nexxyz/cellSymphony/release-artifacts/enclosure/step/standoff_pillar_10mm.step

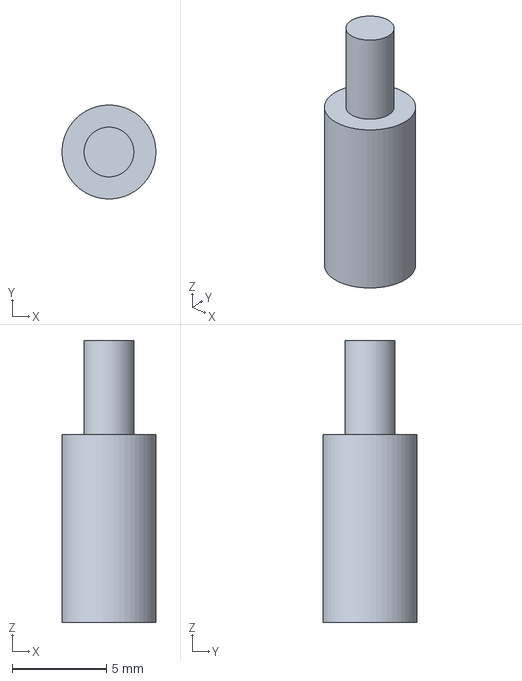
[picture p19: CAD file, 2026-07-09]
release-artifacts/enclosure/step/standoff_pillar_10mm.step
5.00 x 5.00 x 15.0 mm
