nexxyz/cellSymphony/release-artifacts/enclosure/step/standoff_top_pin_thin_base.step

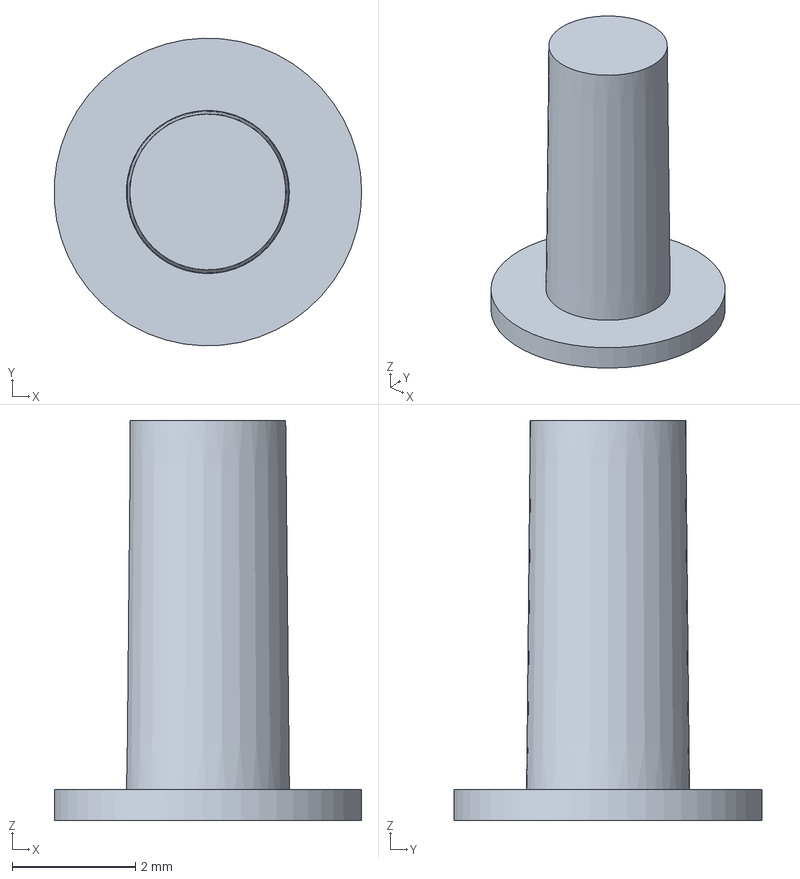
[picture p20: CAD file, 2026-07-08]
release-artifacts/enclosure/step/standoff_top_pin_thin_base.step
5.00 x 5.00 x 6.50 mm
