nexxyz/cellSymphony/release-artifacts/enclosure/3mf-multicolor/mx_keycap_play_multicolor_flush.3mf

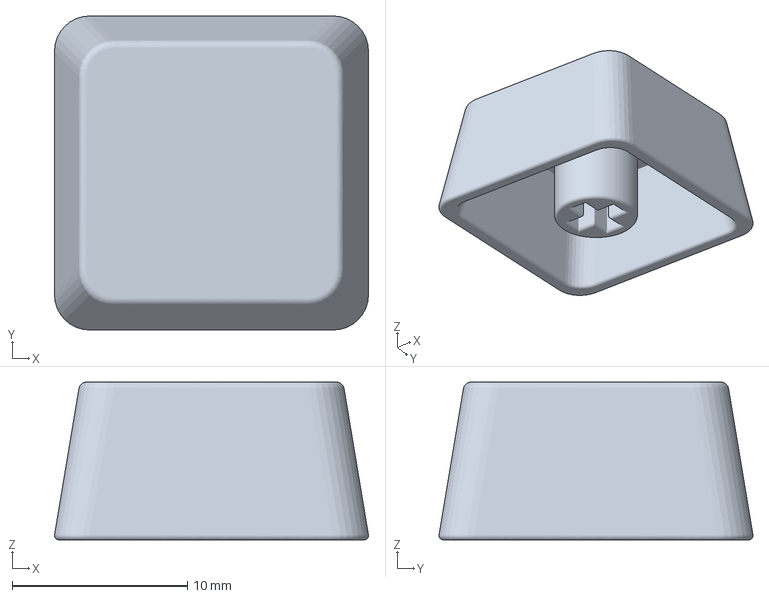
[picture p22: CAD file, 2026-07-10]
release-artifacts/enclosure/3mf-multicolor/mx_keycap_play_multicolor_flush.3mf
17.9 x 17.9 x 9.00 mm
