nexxyz/cellSymphony/userdocs/hardware/images/assembly/audio-breakout.jpg

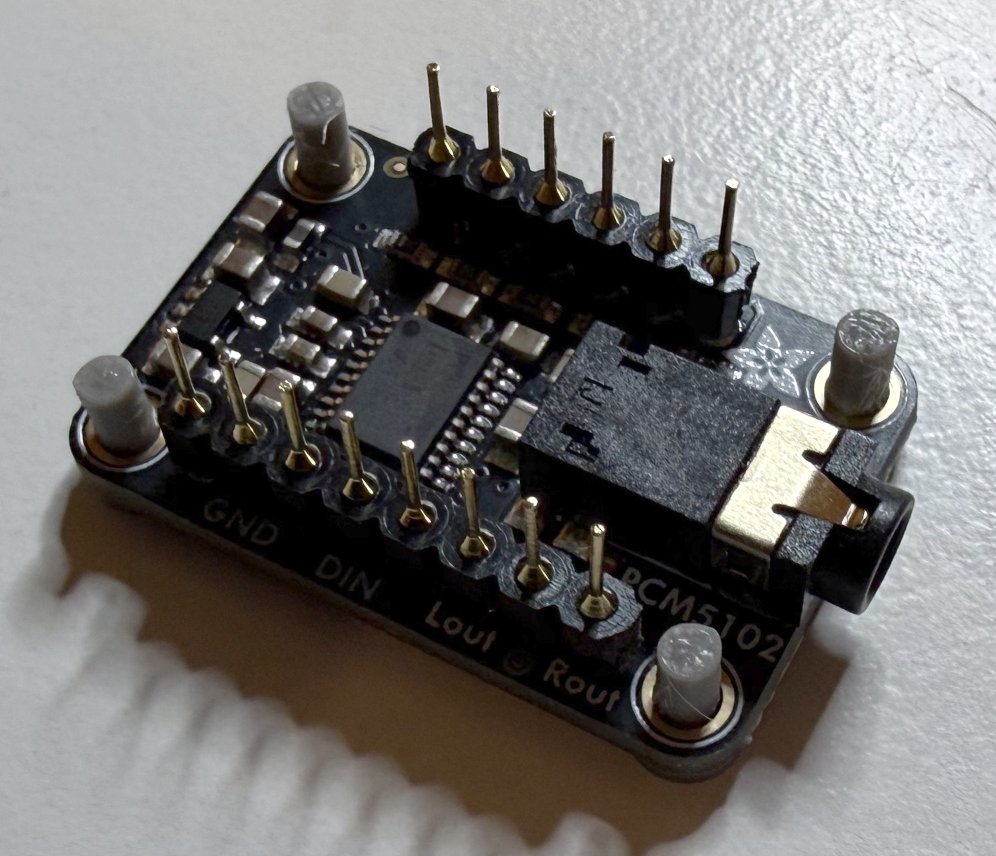
userdocs/hardware/images/assembly/audio-breakout.jpg
