nexxyz/cellSymphony/userdocs/hardware/images/assembly/neotrellis-address-jumpers.jpg

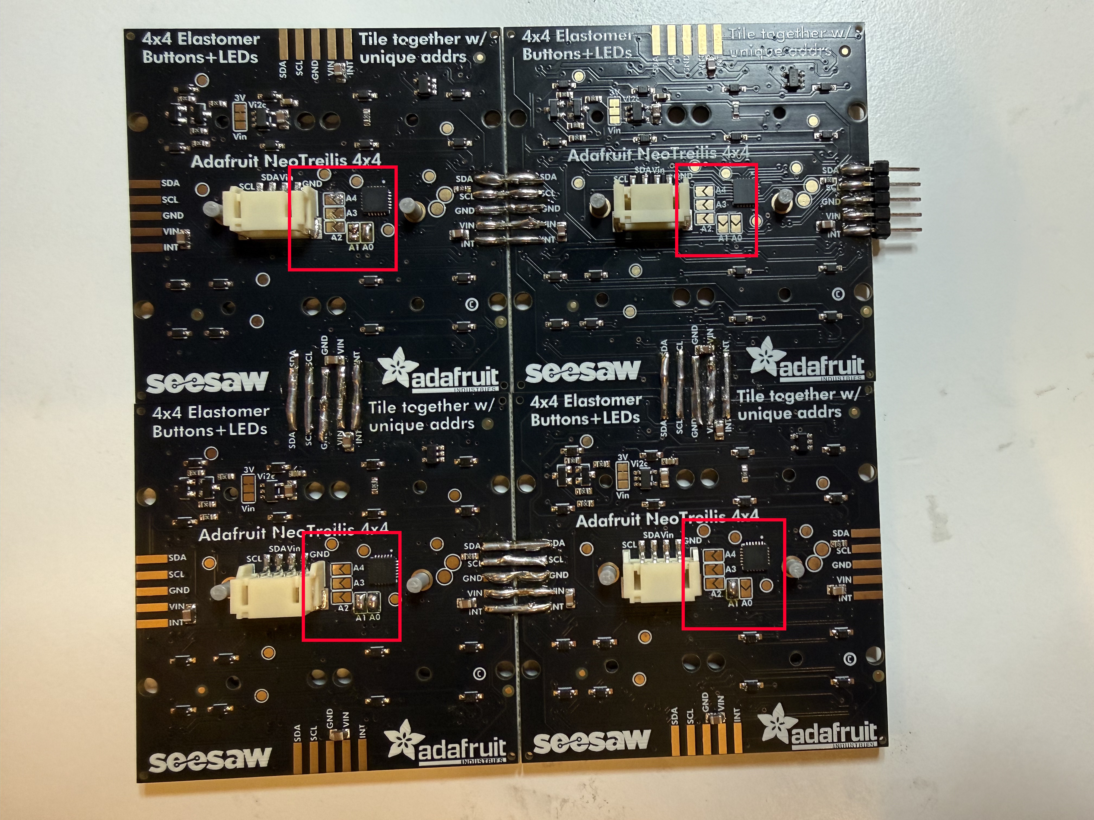
userdocs/hardware/images/assembly/neotrellis-address-jumpers.jpg
