nexxyz/cellSymphony/userdocs/hardware/images/assembly/oled.jpg

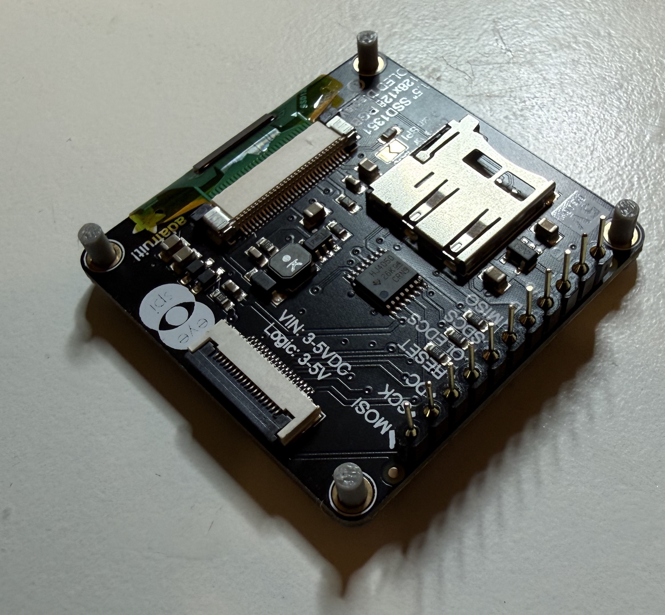
userdocs/hardware/images/assembly/oled.jpg
