nexxyz/cellSymphony/userdocs/hardware/images/assembly/rpi-content-repository.png

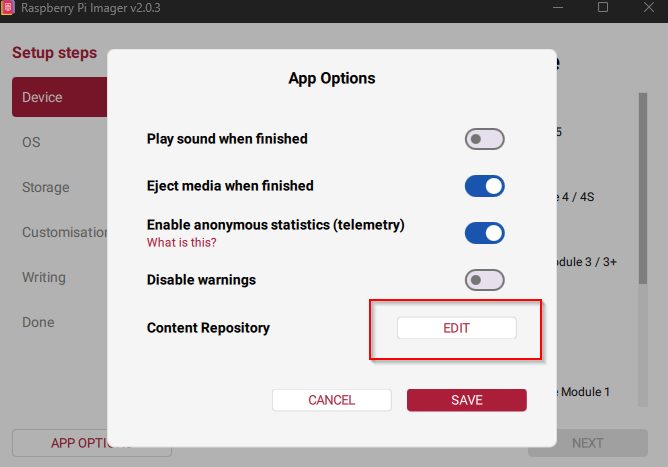
userdocs/hardware/images/assembly/rpi-content-repository.png
