nexxyz/cellSymphony/userdocs/hardware/images/assembly/rpi-imager-options.png

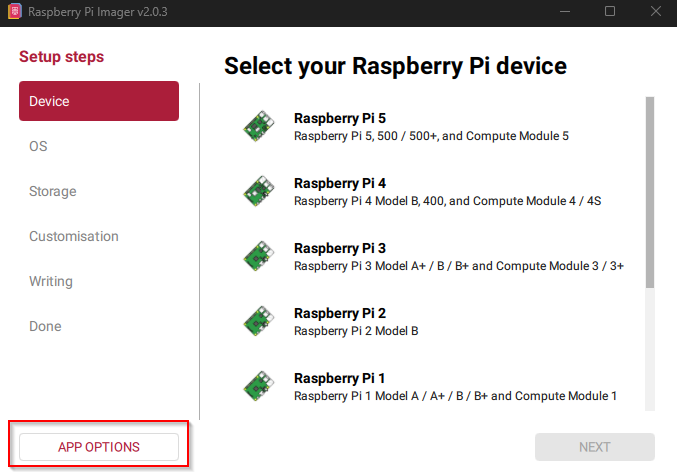
userdocs/hardware/images/assembly/rpi-imager-options.png
