nexxyz/cellSymphony/userdocs/hardware/images/assembly/rpi-repository-source.png

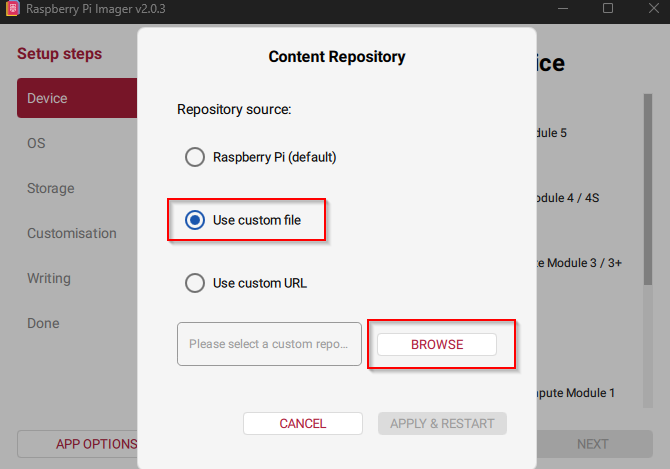
userdocs/hardware/images/assembly/rpi-repository-source.png
