nexxyz/cellSymphony/userdocs/hardware/images/assembly/soldered-pcb.jpg

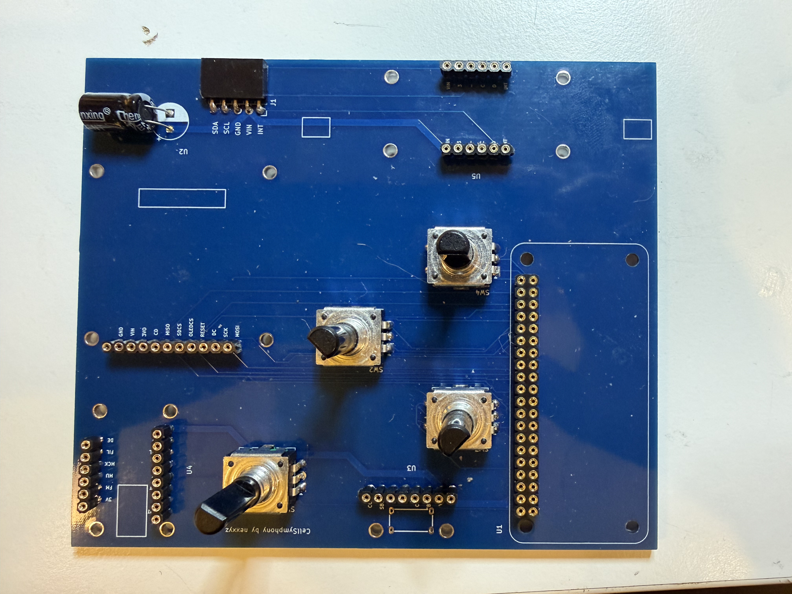
userdocs/hardware/images/assembly/soldered-pcb.jpg
