nexxyz/cellSymphony/apps/pi-zero/src/render.rs

use crate::seesaw_io::SeesawCommand;
use octessera_hal::OledSsd1351;
use platform_core::palette;
use playback_runtime::RuntimeUiPulse;
use serde_json::Value;
use std::sync::mpsc::Sender;
use std::time::{Duration, Instant};

pub(crate) mod hdmi;
mod oled;
mod sleep_leds;

pub(crate) use oled::OLED_FRAME_BYTES;
#[cfg(test)]
use oled::{glyph_rows, oled_frame};
use oled::{oled_frame_into, oled_signature};
use sleep_leds::{SleepLedAnimation, SleepLedFrames};

const SPLASH_BOOT: &[u8] = include_bytes!(concat!(env!("OUT_DIR"), "/splash_boot.rgb565"));
const SPLASH_SLEEP_SHUTDOWN: &[u8] =
    include_bytes!(concat!(env!("OUT_DIR"), "/splash_sleep_shutdown.rgb565"));
const SLEEP_DIM_SCALE: f32 = 0.08;
const MIN_SLEEP_DIM_SCALE: f32 = 0.04;

pub struct HardwareRenderTargets {
    pub oled: OledSsd1351,
    pub seesaw_tx: Sender<SeesawCommand>,
    pub hdmi: Option<hdmi::HdmiFramebuffer>,
}

pub struct HardwareRenderCache {
    led_frame: Option<[[u8; 3]; 64]>,
    neokey_colors: Option<[[u8; 3]; 4]>,
    sleep_leds: SleepLedAnimation,
    oled_signature: u64,
    oled_frame: Vec<u8>,
    hdmi_signature: u64,
    event_dot_until: Option<Instant>,
    transport_flash_until: Option<Instant>,
    transport_flash: Option<String>,
}

impl HardwareRenderCache {
    pub fn new() -> Self {
        Self {
            led_frame: None,
            neokey_colors: None,
            sleep_leds: SleepLedAnimation::new(),
            oled_signature: 0,
            oled_frame: vec![0_u8; OLED_FRAME_BYTES],
            hdmi_signature: 0,
            event_dot_until: None,
            transport_flash_until: None,
            transport_flash: None,
        }
    }

    pub fn apply_ui_pulse(&mut self, pulse: RuntimeUiPulse) {
        let now = Instant::now();
        match pulse {
            RuntimeUiPulse::TriggerPulse { duration_ms } => {
                self.event_dot_until = Some(now + Duration::from_millis(duration_ms));
            }
            RuntimeUiPulse::TransportFlash { flash, duration_ms } => {
                self.transport_flash = Some(flash);
                self.transport_flash_until = Some(now + Duration::from_millis(duration_ms));
            }
        }
    }

    pub fn snapshot_with_transients(&mut self, snapshot: &Value) -> Value {
        let now = Instant::now();
        let event_active = self.event_dot_until.is_some_and(|until| now < until);
        let transport_active = self.transport_flash_until.is_some_and(|until| now < until);
        if !event_active {
            self.event_dot_until = None;
        }
        if !transport_active {
            self.transport_flash_until = None;
            self.transport_flash = None;
        }
        if !event_active && !transport_active {
            return snapshot.clone();
        }
        let mut snapshot = snapshot.clone();
        if event_active {
            snapshot["eventDotOn"] = serde_json::json!(true);
        }
        if transport_active {
            if let Some(flash) = &self.transport_flash {
                snapshot["transportFlash"] = serde_json::json!(flash);
            }
        }
        snapshot
    }
}

impl Default for HardwareRenderCache {
    fn default() -> Self {
        Self::new()
    }
}

pub fn render_snapshot_cached(
    targets: &mut HardwareRenderTargets,
    snapshot: &Value,
    cache: &mut HardwareRenderCache,
) -> Option<Instant> {
    let animation_deadline = if snapshot_display_off(snapshot) {
        let now = Instant::now();
        let settings = snapshot.get("settings").unwrap_or(&Value::Null);
        let entered_sleep = cache.sleep_leds.enter(
            now,
            brightness_scale(settings.get("gridBrightness")),
            brightness_scale(settings.get("buttonBrightness")),
        );
        if entered_sleep {
            let frames = cache.sleep_leds.frames_at(now);
            send_sleep_led_frames(targets, cache, frames);
        } else if let Some(frames) = cache.sleep_leds.frames_if_due(now) {
            send_sleep_led_frames(targets, cache, frames);
        }
        cache.sleep_leds.next_deadline()
    } else {
        if cache.sleep_leds.active() {
            cache.clear_sleep_animation();
        }
        render_normal_leds(targets, snapshot, cache);
        None
    };

    let signature = oled_signature(snapshot);
    if cache.oled_signature != signature {
        cache.oled_signature = signature;
        render_oled(&mut targets.oled, snapshot, &mut cache.oled_frame);
    }

    if let Some(hdmi) = targets.hdmi.as_mut() {
        let signature = hdmi::hdmi_signature(snapshot);
        if cache.hdmi_signature != signature {
            cache.hdmi_signature = signature;
            hdmi.render(snapshot);
        }
    }
    animation_deadline
}

impl HardwareRenderCache {
    fn clear_sleep_animation(&mut self) {
        self.sleep_leds.stop();
        self.led_frame = None;
        self.neokey_colors = None;
    }

    pub(crate) fn render_sleep_tick(
        &mut self,
        targets: &mut HardwareRenderTargets,
        now: Instant,
    ) -> Option<Instant> {
        if !self.sleep_leds.active() {
            return None;
        }
        if let Some(frames) = self.sleep_leds.frames_if_due(now) {
            send_sleep_led_frames(targets, self, frames);
        }
        self.sleep_leds.next_deadline()
    }
}

fn render_normal_leds(
    targets: &mut HardwareRenderTargets,
    snapshot: &Value,
    cache: &mut HardwareRenderCache,
) {
    if let Some(frame) = led_frame(snapshot) {
        send_grid_frame(targets, cache, frame);
    }
    send_neokey_colors(targets, cache, neokey_colors(snapshot));
}

fn send_sleep_led_frames(
    targets: &mut HardwareRenderTargets,
    cache: &mut HardwareRenderCache,
    frames: SleepLedFrames,
) {
    send_grid_frame(targets, cache, frames.grid);
    send_neokey_colors(targets, cache, frames.keys);
}

fn send_grid_frame(
    targets: &mut HardwareRenderTargets,
    cache: &mut HardwareRenderCache,
    frame: [[u8; 3]; 64],
) {
    if cache.led_frame.as_ref() != Some(&frame)
        && targets
            .seesaw_tx
            .send(SeesawCommand::GridFrame(frame))
            .is_ok()
    {
        cache.led_frame = Some(frame);
    }
}

fn send_neokey_colors(
    targets: &mut HardwareRenderTargets,
    cache: &mut HardwareRenderCache,
    colors: [[u8; 3]; 4],
) {
    let previous = cache.neokey_colors.unwrap_or([[u8::MAX; 3]; 4]);
    if previous != colors
        && targets
            .seesaw_tx
            .send(SeesawCommand::NeoKeyColors(colors))
            .is_ok()
    {
        cache.neokey_colors = Some(colors);
    }
}

pub fn led_frame(snapshot: &Value) -> Option<[[u8; 3]; 64]> {
    let settings = snapshot.get("settings").unwrap_or(&Value::Null);
    let mut brightness = brightness_scale(settings.get("gridBrightness"));
    if settings
        .get("ledsDimmed")
        .and_then(Value::as_bool)
        .unwrap_or(false)
    {
        brightness = sleep_dim_brightness(brightness);
    }
    let Some(rgb) = snapshot.get("leds")?.get("rgb").and_then(Value::as_array) else {
        return legacy_led_frame(snapshot, brightness);
    };
    let mut frame = [[0_u8; 3]; 64];
    for (idx, cell) in frame.iter_mut().enumerate() {
        let offset = idx * 3;
        *cell = scale(
            [
                scaled_u8(rgb.get(offset)),
                scaled_u8(rgb.get(offset + 1)),
                scaled_u8(rgb.get(offset + 2)),
            ],
            brightness,
        );
    }
    Some(frame)
}

fn legacy_led_frame(snapshot: &Value, brightness: f32) -> Option<[[u8; 3]; 64]> {
    let cells = snapshot.get("leds")?.get("cells")?.as_array()?;
    let mut frame = [[0_u8; 3]; 64];
    for (idx, cell) in cells.iter().take(64).enumerate() {
        frame[idx] = scale(
            [
                scaled_u8(cell.get("r")),
                scaled_u8(cell.get("g")),
                scaled_u8(cell.get("b")),
            ],
            brightness,
        );
    }
    Some(frame)
}

pub fn neokey_colors(snapshot: &Value) -> [[u8; 3]; 4] {
    let settings = snapshot.get("settings").unwrap_or(&Value::Null);
    let mut button_scale = brightness_scale(settings.get("buttonBrightness"));
    if settings
        .get("ledsDimmed")
        .and_then(Value::as_bool)
        .unwrap_or(false)
    {
        button_scale = sleep_dim_brightness(button_scale);
    }
    let combined = settings
        .get("combinedModifierHeld")
        .and_then(Value::as_bool)
        .unwrap_or(false);
    let shift_held = settings
        .get("shiftHeld")
        .and_then(Value::as_bool)
        .unwrap_or(false);
    let fn_held = settings
        .get("fnHeld")
        .and_then(Value::as_bool)
        .unwrap_or(false);
    let flash = snapshot
        .get("transportFlash")
        .or_else(|| settings.get("transportFlash"))
        .and_then(Value::as_str)
        .unwrap_or("none");
    let icon = snapshot
        .get("transportIcon")
        .and_then(Value::as_str)
        .unwrap_or("stop");
    let back = scale(palette::RED, button_scale);
    let space = if icon == "stop" {
        scale(palette::RED, button_scale)
    } else if icon == "pause" {
        scale(palette::BLUE, button_scale)
    } else if flash == "measure" {
        scale(palette::GREEN, button_scale)
    } else if flash == "beat" {
        scale(palette::YELLOW, button_scale)
    } else {
        scale(dim(palette::GREEN, 3), button_scale)
    };
    let shift = if combined {
        scale(palette::BLUE, button_scale)
    } else if shift_held {
        scale(palette::YELLOW, button_scale)
    } else {
        scale(dim(palette::GRAY, 3), button_scale)
    };
    let func = if combined {
        scale(palette::BLUE, button_scale)
    } else if fn_held {
        scale(palette::YELLOW, button_scale)
    } else {
        scale(dim(palette::GRAY, 3), button_scale)
    };
    [back, space, shift, func]
}

fn render_oled(oled: &mut OledSsd1351, snapshot: &Value, frame: &mut [u8]) {
    let off = snapshot_display_off(snapshot);
    if !off {
        let _ = oled.display_on();
    }
    oled_frame_into(snapshot, frame);
    let _ = oled.write_frame(frame);
    if off {
        let _ = oled.display_off();
    }
}

pub fn render_boot_splash(oled: &mut OledSsd1351) {
    let _ = oled.display_on();
    let snapshot = serde_json::json!({
        "display": {
            "off": false,
            "splash": "startup",
            "toast": ""
        },
        "settings": { "displayBrightness": 100 }
    });
    let mut frame = vec![0_u8; OLED_FRAME_BYTES];
    render_oled(oled, &snapshot, &mut frame);
}

pub fn render_shutdown_splash(oled: &mut OledSsd1351) {
    let _ = oled.display_on();
    let snapshot = serde_json::json!({
        "display": {
            "off": false,
            "splash": "shutdown",
            "toast": ""
        },
        "settings": { "displayBrightness": 100 }
    });
    let mut frame = vec![0_u8; OLED_FRAME_BYTES];
    render_oled(oled, &snapshot, &mut frame);
}

fn snapshot_display_off(snapshot: &Value) -> bool {
    snapshot
        .get("display")
        .and_then(|display| display.get("off"))
        .and_then(Value::as_bool)
        .unwrap_or(false)
}

pub(crate) fn fault_oled_frame_into(lines: &[String], frame: &mut [u8], lit: bool) {
    oled::fault_frame_into(lines, frame, lit);
}

fn scaled_u8(value: Option<&Value>) -> u8 {
    value.and_then(Value::as_u64).unwrap_or(0).min(255) as u8
}

fn brightness_scale(value: Option<&Value>) -> f32 {
    value
        .and_then(Value::as_u64)
        .map(|value| value.min(100) as f32 / 100.0)
        .unwrap_or(1.0)
}

fn sleep_dim_brightness(brightness: f32) -> f32 {
    if brightness <= 0.0 {
        0.0
    } else {
        (brightness * SLEEP_DIM_SCALE).max(MIN_SLEEP_DIM_SCALE)
    }
}

#[rustfmt::skip]
pub(super) fn scale(rgb: [u8; 3], factor: f32) -> [u8; 3] { [
    ((rgb[0] as f32) * factor).round().clamp(0.0, 255.0) as u8,
    ((rgb[1] as f32) * factor).round().clamp(0.0, 255.0) as u8,
    ((rgb[2] as f32) * factor).round().clamp(0.0, 255.0) as u8,
] }

pub(super) fn dim(rgb: [u8; 3], divisor: u8) -> [u8; 3] {
    let divisor = divisor.max(1);
    [rgb[0] / divisor, rgb[1] / divisor, rgb[2] / divisor]
}

pub(super) fn rgb565(rgb: [u8; 3]) -> u16 {
    ((u16::from(rgb[0]) & 0xF8) << 8) | ((u16::from(rgb[1]) & 0xFC) << 3) | (u16::from(rgb[2]) >> 3)
}

#[cfg(test)]
mod tests;
