nexxyz/cellSymphony/crates/playback-runtime/src/native_menu/pulses_sections.rs

use super::{
    action_item, axis_binding_label, bool_item, enum_item, enum_item_from_strings, group,
    number_item, parameter_picker_group_numeric, selected_index, slot_option_selected,
    NativeLinkArpConfig, NativeLinkLfoConfig, NativeMenuAction, NativeMenuConfig, NativeMenuItem,
    NativePulsesLayerConfig,
};

pub(super) fn arp_group(prefix: &str, arp: &NativeLinkArpConfig) -> NativeMenuItem {
    group(
        "Arp",
        vec![
            enum_item(
                "Mode",
                format!("{prefix}.mode"),
                vec![
                    "none",
                    "direct",
                    "up",
                    "down",
                    "bounce",
                    "outside_in",
                    "rotating",
                    "random",
                    "octave_spread",
                    "chord_strike",
                    "strum",
                ],
                selected_index(
                    &[
                        "none",
                        "direct",
                        "up",
                        "down",
                        "bounce",
                        "outside_in",
                        "rotating",
                        "random",
                        "octave_spread",
                        "chord_strike",
                        "strum",
                    ],
                    &arp.mode,
                ),
            ),
            enum_item(
                "Source",
                format!("{prefix}.source"),
                vec!["simultaneous", "held"],
                selected_index(&["simultaneous", "held"], &arp.source),
            ),
            number_item(
                "Step",
                format!("{prefix}.stepIntervalSteps"),
                i32::from(arp.step_interval_steps),
                1,
                16,
                1,
            ),
            number_item(
                "Length ms",
                format!("{prefix}.noteLengthMs"),
                i32::from(arp.note_length_ms),
                10,
                2000,
                10,
            ),
            number_item(
                "Gate %",
                format!("{prefix}.gatePct"),
                i32::from(arp.gate_pct),
                1,
                100,
                1,
            ),
            number_item(
                "Octaves",
                format!("{prefix}.octaveSpread"),
                i32::from(arp.octave_spread),
                0,
                3,
                1,
            ),
        ],
    )
}

pub(super) fn link_lfo_group(
    label: String,
    prefix: &str,
    lfo: &NativeLinkLfoConfig,
    config: &NativeMenuConfig,
) -> NativeMenuItem {
    group(
        label,
        vec![
            bool_item("Enabled", format!("{prefix}.enabled"), lfo.enabled),
            parameter_picker_group_numeric(
                axis_binding_label("Target", lfo.target.as_ref()),
                format!("{prefix}.target"),
                lfo.target.as_ref(),
                config,
            ),
            enum_item(
                "Period",
                format!("{prefix}.period"),
                crate::timing_units::NOTE_UNIT_OPTIONS.to_vec(),
                selected_index(crate::timing_units::NOTE_UNIT_OPTIONS, &lfo.period),
            ),
            number_item(
                "Depth %",
                format!("{prefix}.depthPct"),
                i32::from(lfo.depth_pct),
                0,
                100,
                1,
            ),
        ],
    )
}

pub(super) fn global_link_lfos_group(config: &NativeMenuConfig) -> NativeMenuItem {
    group(
        "LFOs",
        config
            .link_lfos
            .iter()
            .enumerate()
            .map(|(index, lfo)| {
                link_lfo_group(
                    format!("L{}", index + 1),
                    &format!("linkLfos.{index}"),
                    lfo,
                    config,
                )
            })
            .collect(),
    )
}

pub(super) fn scanning_group(
    prefix: &str,
    sense: &NativePulsesLayerConfig,
    instrument_options: &[String],
) -> NativeMenuItem {
    let mut children = vec![enum_item(
        "Scan Mode",
        format!("{prefix}.scanMode"),
        vec!["none", "scanning"],
        selected_index(&["none", "scanning"], &sense.scan_mode),
    )];
    if sense.scan_mode == "scanning" {
        children.extend(vec![
            enum_item(
                "Scan Axis",
                format!("{prefix}.scanAxis"),
                vec!["rows", "columns"],
                selected_index(&["rows", "columns"], &sense.scan_axis),
            ),
            enum_item(
                "Scan Unit",
                format!("{prefix}.scanUnit"),
                crate::timing_units::NOTE_UNIT_OPTIONS.to_vec(),
                selected_index(crate::timing_units::NOTE_UNIT_OPTIONS, &sense.scan_unit),
            ),
            enum_item(
                "Scan Direction",
                format!("{prefix}.scanDirection"),
                vec!["forward", "reverse"],
                selected_index(&["forward", "reverse"], &sense.scan_direction),
            ),
            enum_item(
                "Sections",
                format!("{prefix}.scanSections"),
                vec!["1", "2", "4", "8"],
                selected_index(&["1", "2", "4", "8"], &sense.scan_sections.to_string()),
            ),
            enum_item_from_strings(
                "Instrument",
                format!("{prefix}.mapping.scanned.slot"),
                instrument_options.to_vec(),
                slot_option_selected(sense.scanned_slot, instrument_options.len()),
            ),
            enum_item(
                "Action",
                format!("{prefix}.mapping.scanned.action"),
                vec!["none", "note_on", "note_off"],
                selected_index(&["none", "note_on", "note_off"], &sense.scanned_action),
            ),
            timing_item(
                "Scan Delay",
                format!("{prefix}.mapping.scanned.delaySteps"),
                sense.scanned_timing.delay_steps,
                16,
            ),
            timing_item(
                "Scan Retrig",
                format!("{prefix}.mapping.scanned.retriggerCount"),
                sense.scanned_timing.retrigger_count,
                8,
            ),
            enum_item_from_strings(
                "Empty Inst",
                format!("{prefix}.mapping.scanned_empty.slot"),
                instrument_options.to_vec(),
                slot_option_selected(sense.scanned_empty_slot, instrument_options.len()),
            ),
            enum_item(
                "Empty Trig",
                format!("{prefix}.mapping.scanned_empty.action"),
                vec!["none", "note_on", "note_off"],
                selected_index(
                    &["none", "note_on", "note_off"],
                    &sense.scanned_empty_action,
                ),
            ),
            timing_item(
                "Empty Delay",
                format!("{prefix}.mapping.scanned_empty.delaySteps"),
                sense.scanned_empty_timing.delay_steps,
                16,
            ),
            timing_item(
                "Empty Retrig",
                format!("{prefix}.mapping.scanned_empty.retriggerCount"),
                sense.scanned_empty_timing.retrigger_count,
                8,
            ),
        ]);
    }
    group("Scanning", children)
}

pub(super) fn events_group(
    prefix: &str,
    sense: &NativePulsesLayerConfig,
    instrument_options: &[String],
) -> NativeMenuItem {
    let mut children = vec![
        bool_item(
            "Event Triggers",
            format!("{prefix}.eventEnabled"),
            sense.event_enabled,
        ),
        bool_item(
            "State Notes",
            format!("{prefix}.stateNotesEnabled"),
            sense.state_notes_enabled,
        ),
    ];
    children.extend(event_mapping_item(
        prefix,
        "Activate",
        "activate",
        sense.activate_slot,
        &sense.activate_action,
        sense.activate_timing,
        instrument_options,
    ));
    children.extend(event_mapping_item(
        prefix,
        "Stable",
        "stable",
        sense.stable_slot,
        &sense.stable_action,
        sense.stable_timing,
        instrument_options,
    ));
    children.extend(event_mapping_item(
        prefix,
        "Deactivate",
        "deactivate",
        sense.deactivate_slot,
        &sense.deactivate_action,
        sense.deactivate_timing,
        instrument_options,
    ));
    group("Events", children)
}

pub(super) fn trigger_probability_group(
    index: usize,
    prefix: &str,
    sense: &NativePulsesLayerConfig,
) -> NativeMenuItem {
    group(
        "Trigger Prob.",
        vec![
            enum_item(
                "Mode",
                format!("{prefix}.triggerProbabilityMode"),
                vec!["zero", "custom", "full"],
                selected_index(&["zero", "custom", "full"], &sense.trigger_probability_mode),
            ),
            number_item(
                "Prob Low",
                format!("{prefix}.triggerProbabilityLowPct"),
                i32::from(sense.trigger_probability_low_pct),
                0,
                100,
                1,
            ),
            number_item(
                "Prob High",
                format!("{prefix}.triggerProbabilityHighPct"),
                i32::from(sense.trigger_probability_high_pct),
                0,
                100,
                1,
            ),
            action_item(
                "Map Prob Grid",
                format!("{prefix}.triggerProbability.map"),
                NativeMenuAction::PlatformEffect(format!("trigger.probability.assign:{index}")),
            ),
        ],
    )
}

pub(super) fn note_mapping_group(prefix: &str, sense: &NativePulsesLayerConfig) -> NativeMenuItem {
    group(
        "Note Mapping",
        vec![
            number_item(
                "Low Note",
                format!("{prefix}.pitch.lowestNote"),
                i32::from(sense.lowest_note),
                0,
                127,
                1,
            ),
            number_item(
                "High Note",
                format!("{prefix}.pitch.highestNote"),
                i32::from(sense.highest_note),
                0,
                127,
                1,
            ),
            number_item(
                "Start Note",
                format!("{prefix}.pitch.startingNote"),
                i32::from(sense.starting_note),
                0,
                127,
                1,
            ),
            enum_item(
                "Scale",
                format!("{prefix}.pitch.scale"),
                vec![
                    "chromatic",
                    "major",
                    "natural_minor",
                    "dorian",
                    "mixolydian",
                    "major_pentatonic",
                    "minor_pentatonic",
                    "harmonic_minor",
                ],
                selected_index(
                    &[
                        "chromatic",
                        "major",
                        "natural_minor",
                        "dorian",
                        "mixolydian",
                        "major_pentatonic",
                        "minor_pentatonic",
                        "harmonic_minor",
                    ],
                    &sense.scale,
                ),
            ),
            enum_item(
                "Root",
                format!("{prefix}.pitch.root"),
                vec![
                    "C", "C#", "D", "D#", "E", "F", "F#", "G", "G#", "A", "A#", "B",
                ],
                selected_index(
                    &[
                        "C", "C#", "D", "D#", "E", "F", "F#", "G", "G#", "A", "A#", "B",
                    ],
                    &sense.root,
                ),
            ),
            enum_item(
                "Out of Range",
                format!("{prefix}.pitch.outOfRange"),
                vec!["clamp", "wrap"],
                selected_index(&["clamp", "wrap"], &sense.out_of_range),
            ),
        ],
    )
}

fn event_mapping_item(
    prefix: &str,
    label: &str,
    key: &str,
    slot: usize,
    action: &str,
    timing: super::LinkEventTimingConfig,
    instrument_options: &[String],
) -> Vec<NativeMenuItem> {
    let short_label = match label {
        "Activate" => "On",
        "Stable" => "Hold",
        "Deactivate" => "Off",
        _ => label,
    };
    vec![
        enum_item_from_strings(
            format!("{short_label} Inst"),
            format!("{prefix}.mapping.{key}.slot"),
            instrument_options.to_vec(),
            slot_option_selected(slot, instrument_options.len()),
        ),
        enum_item(
            format!("{short_label} Trig"),
            format!("{prefix}.mapping.{key}.action"),
            vec!["none", "note_on", "note_off"],
            selected_index(&["none", "note_on", "note_off"], action),
        ),
        timing_item(
            format!("{short_label} Delay"),
            format!("{prefix}.mapping.{key}.delaySteps"),
            timing.delay_steps,
            16,
        ),
        timing_item(
            format!("{short_label} Retrig"),
            format!("{prefix}.mapping.{key}.retriggerCount"),
            timing.retrigger_count,
            8,
        ),
    ]
}

fn timing_item(label: impl Into<String>, key: String, value: u8, max: i32) -> NativeMenuItem {
    number_item(label, key, i32::from(value), 0, max, 1)
}
