nexxyz/cellSymphony/crates/playback-runtime/src/native_runner/device_input.rs

use crate::protocol::{RunnerMessage, RuntimePlatformEffect};
use std::sync::OnceLock;
use std::time::{Instant, SystemTime, UNIX_EPOCH};

use super::algorithm::LinkRoutingInput;
use super::{
    display_layer_index_from_y, DeviceInput, NativeRunner, NativeToast, RuntimeTransportState,
    SyncSource,
};

impl NativeRunner {
    fn refresh_modifier_state(&mut self) {
        let was_fn_held = self.display.ui.fn_held;
        let was_modifier_held = self.display.ui.fn_held
            || self.display.ui.shift_held
            || self.display.ui.combined_modifier_held;
        self.display.ui.combined_modifier_held = self.display.ui.combined_button_pressed
            || (self.display.ui.fn_button_pressed && self.display.ui.shift_button_pressed);
        self.display.ui.fn_held =
            self.display.ui.fn_button_pressed && !self.display.ui.combined_modifier_held;
        self.display.ui.shift_held =
            self.display.ui.shift_button_pressed && !self.display.ui.combined_modifier_held;
        let modifier_held = self.display.ui.fn_held
            || self.display.ui.shift_held
            || self.display.ui.combined_modifier_held;
        if self.display.ui.fn_held && !was_fn_held {
            self.display.fn_hold_started_at = Some(Instant::now());
        } else if !self.display.ui.fn_held {
            self.display.fn_hold_started_at = None;
        }
        if modifier_held && !was_modifier_held {
            self.display.modifier_hint_started_at = Some(Instant::now());
        } else if !modifier_held {
            self.display.modifier_hint_started_at = None;
        }
    }

    fn mark_modifier_consumed(&mut self) {
        if self.display.ui.fn_held
            || self.display.ui.shift_held
            || self.display.ui.combined_modifier_held
        {
            self.display.modifier_hint_started_at = None;
        }
    }

    pub(super) fn handle_device_input(
        &mut self,
        input: DeviceInput,
    ) -> Result<Vec<RunnerMessage>, String> {
        if self.display.oled_mode == super::NativeOledMode::Splash
            && self.display.oled_splash_text == super::OLED_STARTUP_SPLASH_KEY
        {
            self.advance_oled_sleep_state();
        }
        let trace_context = WakeTraceContext::capture(self, &input);
        if self.display.startup_splash_presented
            && self.display.oled_mode == super::NativeOledMode::Splash
            && self.display.oled_splash_text == super::OLED_STARTUP_SPLASH_KEY
        {
            trace_device_input_wake(trace_context.as_ref(), false, true, "startup_splash");
            return self.messages_with_forced_snapshot();
        }
        let woke_display = self.record_display_interaction();
        if woke_display {
            trace_device_input_wake(trace_context.as_ref(), true, true, "wake_consumed");
            return self.messages_with_forced_snapshot();
        }
        trace_device_input_wake(trace_context.as_ref(), false, false, "active_dispatch");
        if self.display.confirm_dialog.is_some() {
            return self.handle_confirm_device_input(input);
        }
        if self.display.usb_sd_transfer_modal.is_some() {
            return self.handle_usb_sd_transfer_modal_input(input);
        }
        if self.display.system_info_modal.is_some() {
            return self.handle_system_info_modal_input(input);
        }
        let is_modifier_input = matches!(
            input,
            DeviceInput::ButtonShift { .. }
                | DeviceInput::ButtonFn { .. }
                | DeviceInput::ButtonCombinedModifier { .. }
        );
        let result = match input {
            DeviceInput::GridPress { x, y } => self.handle_grid_press_input(x, y),
            DeviceInput::GridRelease { x, y } => self.handle_grid_release_input(x, y),
            DeviceInput::BehaviorAction(action) => {
                let result = self.trigger_behavior_action_result(action.action_type)?;
                self.messages_with_input_result(result)
            }
            DeviceInput::ButtonS { pressed } => self.handle_button_s_input(pressed),
            DeviceInput::ButtonShift { pressed } => {
                self.display.ui.shift_button_pressed = pressed.unwrap_or(false);
                self.refresh_modifier_state();
                self.messages_with_snapshot()
            }
            DeviceInput::ButtonFn { pressed } => {
                self.display.ui.fn_button_pressed = pressed.unwrap_or(false);
                self.refresh_modifier_state();
                self.messages_with_snapshot()
            }
            DeviceInput::ButtonCombinedModifier { pressed } => {
                self.display.ui.combined_button_pressed = pressed.unwrap_or(false);
                self.refresh_modifier_state();
                self.messages_with_snapshot()
            }
            DeviceInput::EncoderTurn { delta, id } => {
                if let Some(index) = Self::aux_index(id.as_deref()) {
                    self.handle_aux_turn(index, delta)?;
                } else if id.as_deref().unwrap_or("main") == "main" && delta != 0 {
                    if self.display.help_popup.is_some() {
                        self.turn_help_popup(delta);
                    } else if self.display.ui.fn_held && delta > 0 {
                        return self.handle_single_step_input();
                    } else if self.display.ui.fn_held {
                    } else {
                        let editing = self.menu.state.editing;
                        let editing_key = if editing {
                            self.menu.current_key().map(str::to_owned)
                        } else {
                            None
                        };
                        self.reset_menu_scroll();
                        self.menu.turn(delta);
                        if let Some(key) = editing_key {
                            self.apply_or_schedule_menu_key(&key)?;
                        }
                    }
                }
                self.messages_with_snapshot()
            }
            DeviceInput::EncoderPress { id } => self.handle_encoder_press_input(id.as_deref()),
            DeviceInput::ButtonA { pressed } => self.handle_button_a_input(pressed),
            DeviceInput::Other => self.messages_with_snapshot(),
        };
        if !is_modifier_input {
            self.mark_modifier_consumed();
        }
        result
    }

    fn handle_confirm_device_input(
        &mut self,
        input: DeviceInput,
    ) -> Result<Vec<RunnerMessage>, String> {
        match input {
            DeviceInput::EncoderTurn { delta, id } if id.as_deref().unwrap_or("main") == "main" => {
                self.turn_confirm_dialog(delta);
            }
            DeviceInput::EncoderPress { id } if id.as_deref().unwrap_or("main") == "main" => {
                if let Some(effect) = self.confirm_dialog_selection()? {
                    return self.messages_with_effects(vec![effect]);
                }
            }
            DeviceInput::ButtonA { pressed } if pressed.unwrap_or(true) => {
                self.display.confirm_dialog = None;
                self.display.toast = Some(NativeToast {
                    message: "Cancelled".into(),
                    offset: 0,
                });
            }
            _ => {}
        }
        self.messages_with_snapshot()
    }
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
